cklopotic/BeerScale/docs/adafruit_products_28ctpschem.png

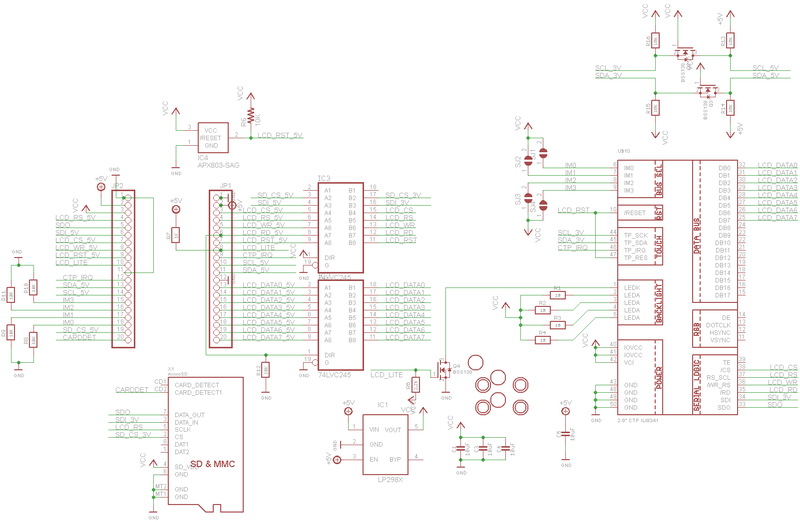
docs/adafruit_products_28ctpschem.png
