cklopotic/BeerScale/pictures/20230804_072641.jpg

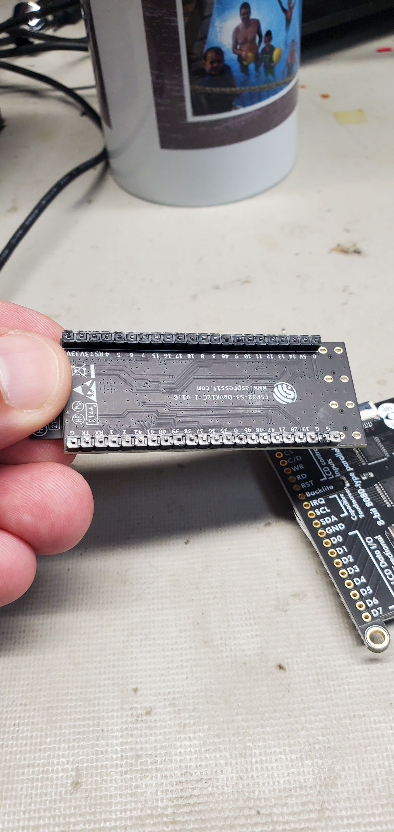
pictures/20230804_072641.jpg
