cklopotic/BeerScale/pictures/20230804_074405.jpg

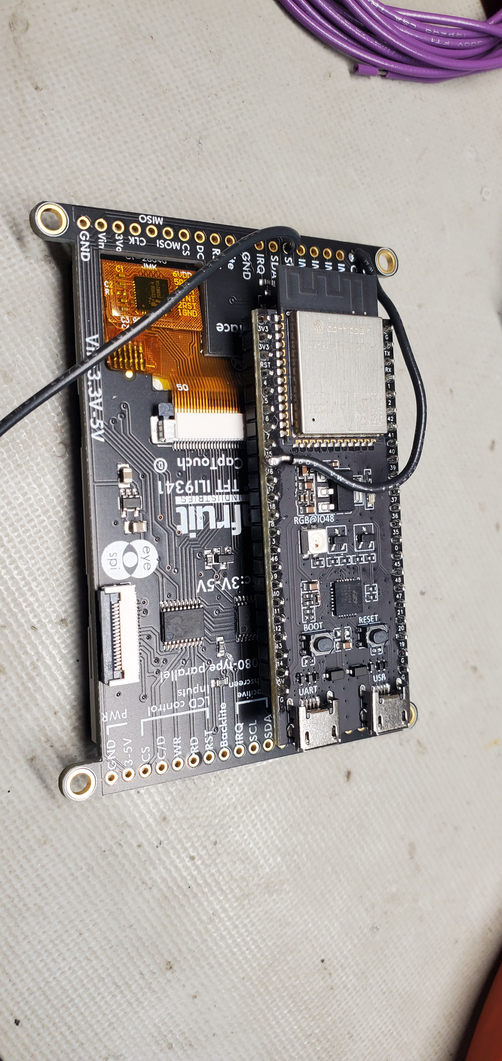
pictures/20230804_074405.jpg
