cklopotic/BeerScale/pictures/20230804_090111.jpg

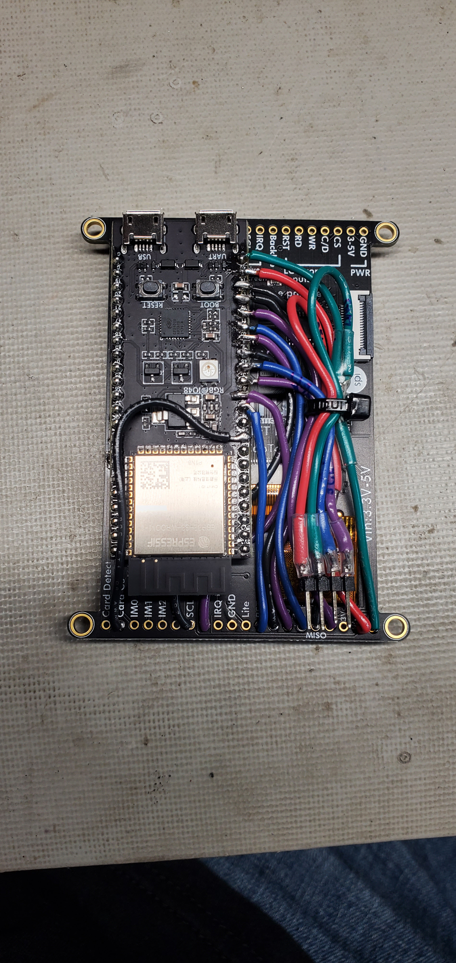
pictures/20230804_090111.jpg
