cklopotic/BeerScale/pictures/20230804_090410.jpg

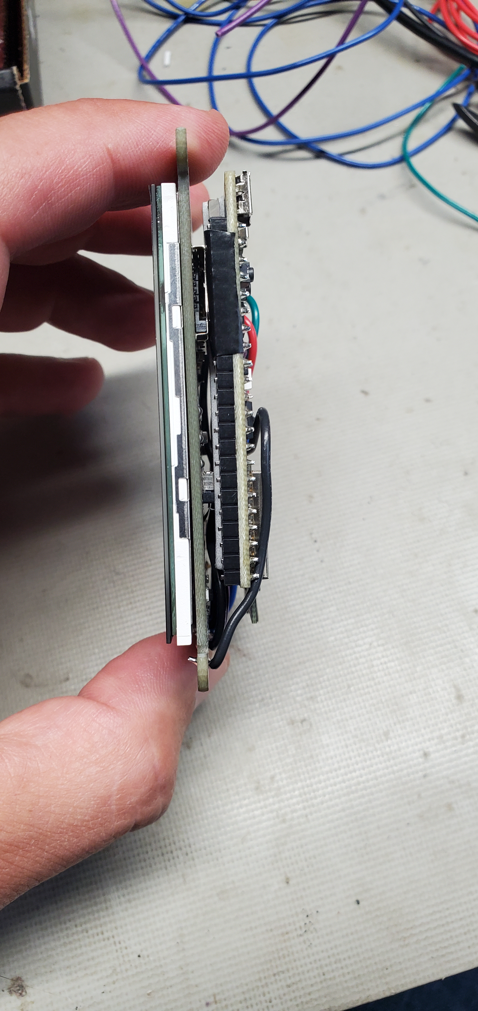
pictures/20230804_090410.jpg
