cklopotic/BeerScale/pictures/20230804_090416.jpg

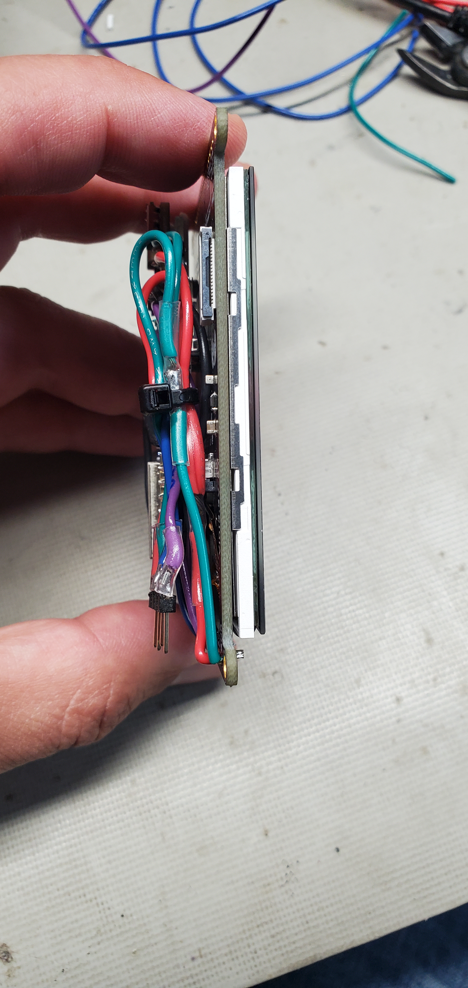
pictures/20230804_090416.jpg
