cklopotic/BeerScale/pictures/20230804_110030.jpg

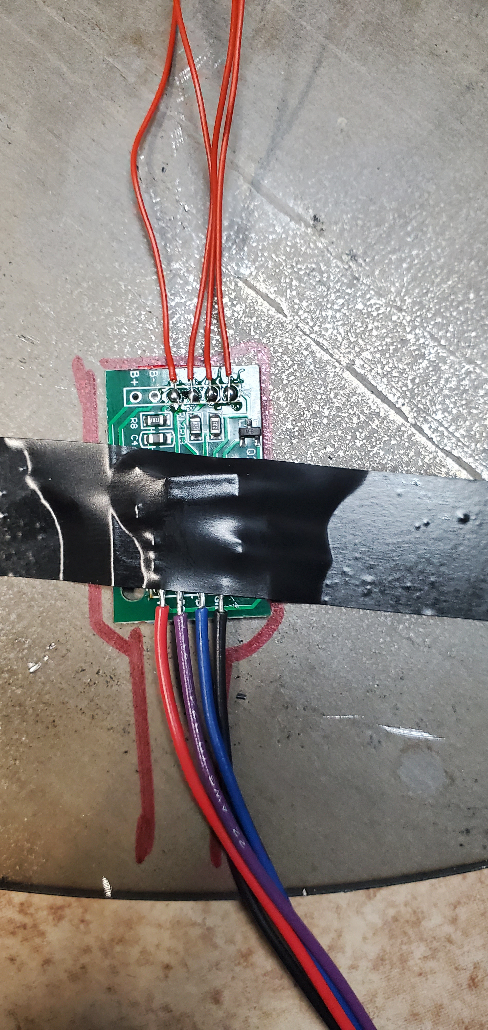
pictures/20230804_110030.jpg
