cklopotic/BeerScale/pictures/IMG_2379.jpg

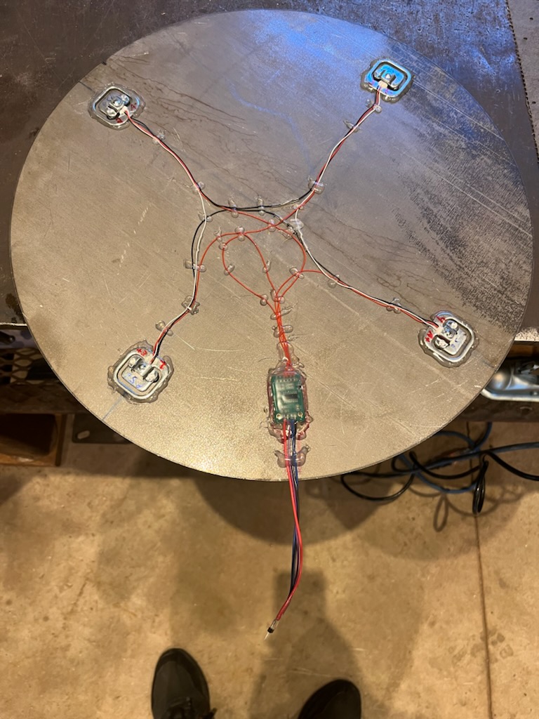
pictures/IMG_2379.jpg
