cklopotic/BeerScale/pictures/IMG_2381.jpg

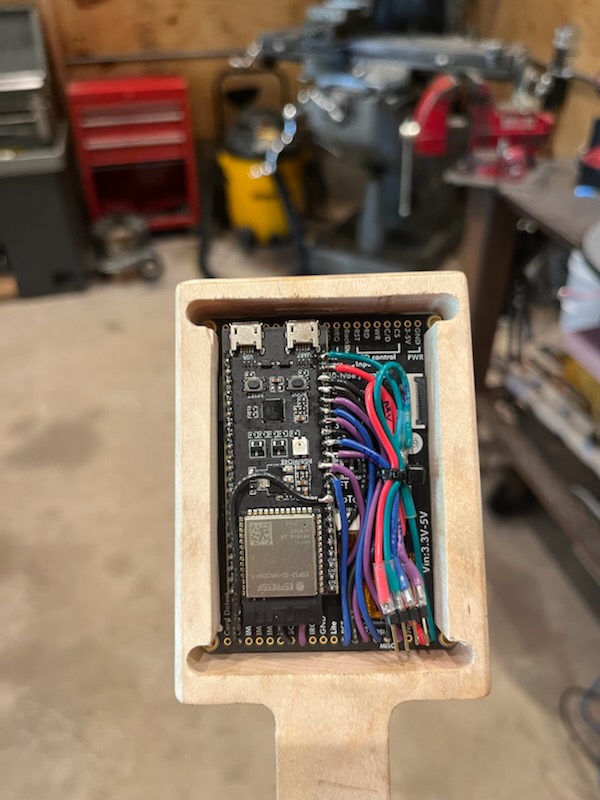
pictures/IMG_2381.jpg
