cklopotic/BeerScale/pictures/IMG_2382.jpg

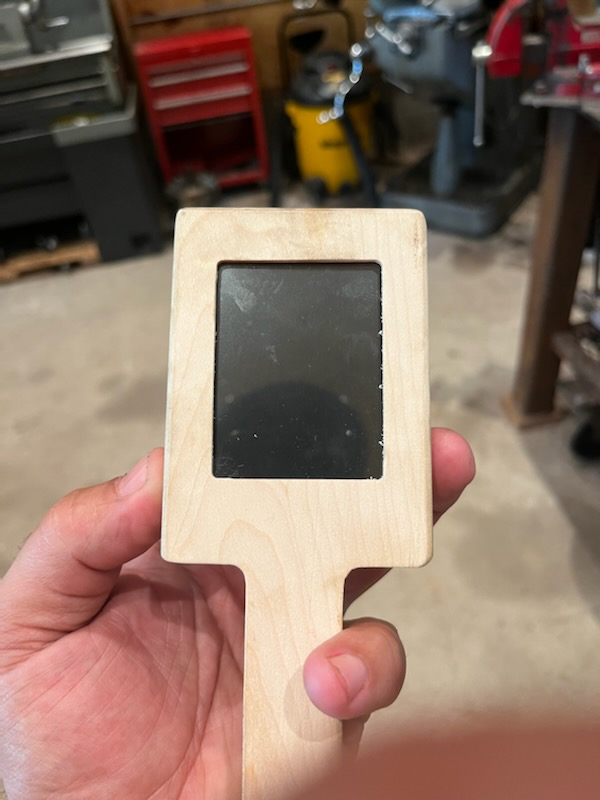
pictures/IMG_2382.jpg
